nullvalue0/WiRSa/Pictures/2024-12-23T05_33_06.740Z-IMG_20241222_194014_2~2.jpg

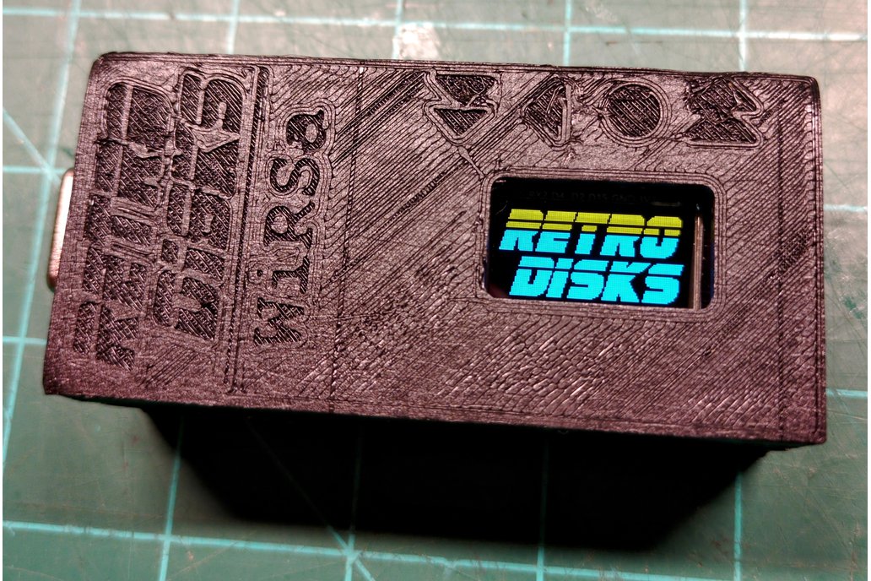
Pictures/2024-12-23T05_33_06.740Z-IMG_20241222_194014_2~2.jpg
