nullvalue0/WiRSa/Pictures/2024-12-23T05_37_01.366Z-IMG_20241222_223214_2~2.jpg

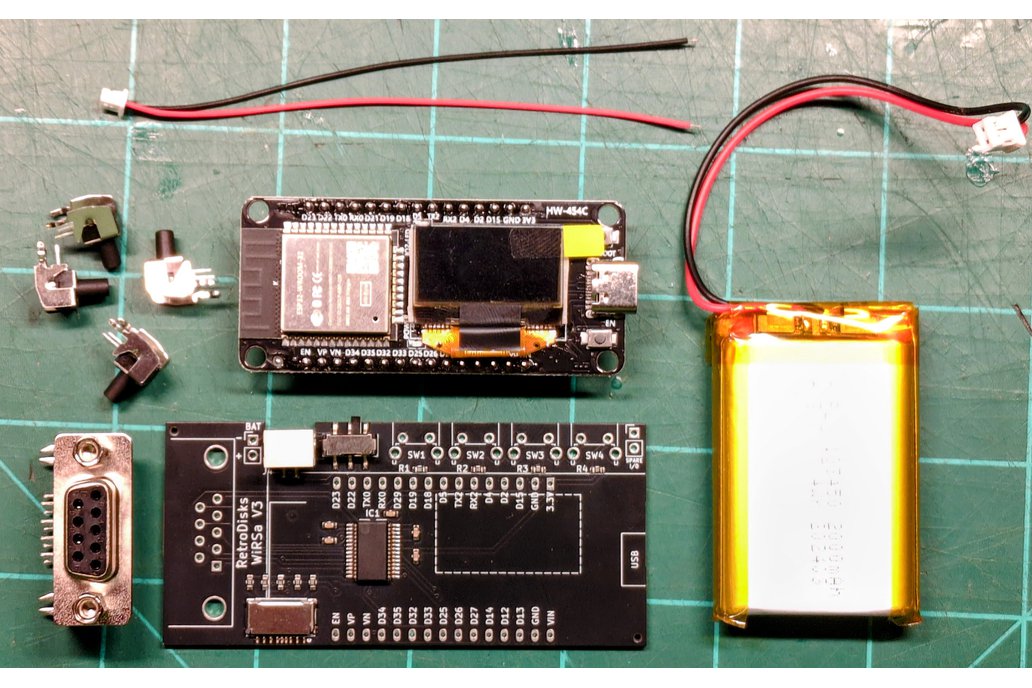
Pictures/2024-12-23T05_37_01.366Z-IMG_20241222_223214_2~2.jpg
