nullvalue0/WiRSa/Pictures/2024-12-24T02_32_21.541Z-IMG_20241223_105522_2~2(1).jpg

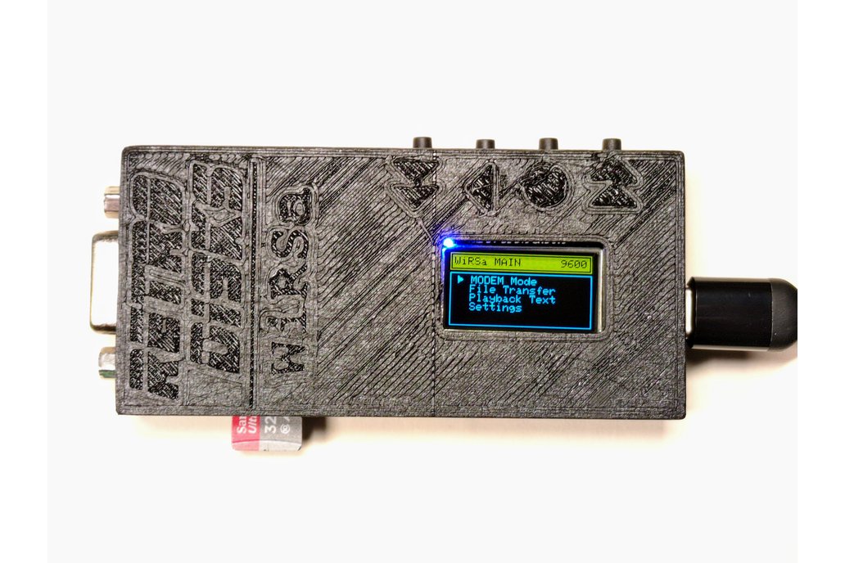
Pictures/2024-12-24T02_32_21.541Z-IMG_20241223_105522_2~2(1).jpg
