nullvalue0/WiRSa/Pictures/IMG_20241208_202616_2~2.jpg

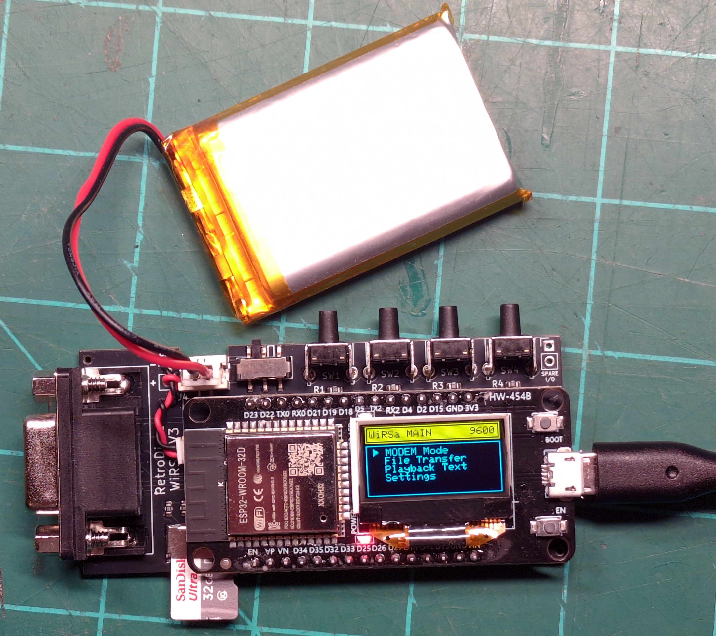
Pictures/IMG_20241208_202616_2~2.jpg
