nullvalue0/WiRSa/Pictures/PXL_20241209_022049034~2.jpg

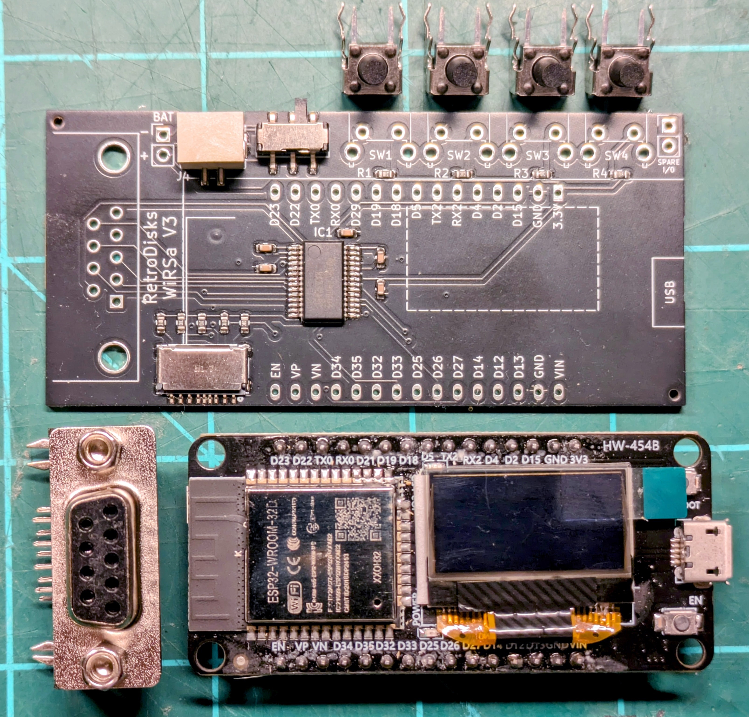
Pictures/PXL_20241209_022049034~2.jpg
