nullvalue0/WiRSa/Pictures/readme_image1.jpg

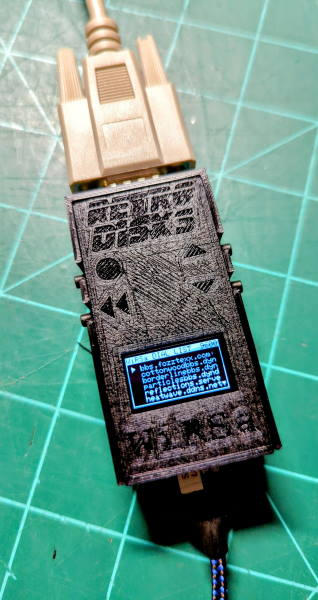
Pictures/readme_image1.jpg
