nullvalue0/WiRSa/Pictures/readme_image3.jpg

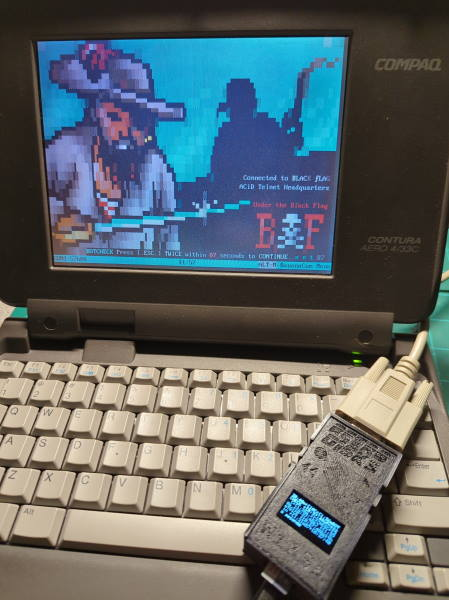
Pictures/readme_image3.jpg
