nullvalue0/WiRSa/Pictures/v2-IMG_20221031_160522~2 (8).jpg

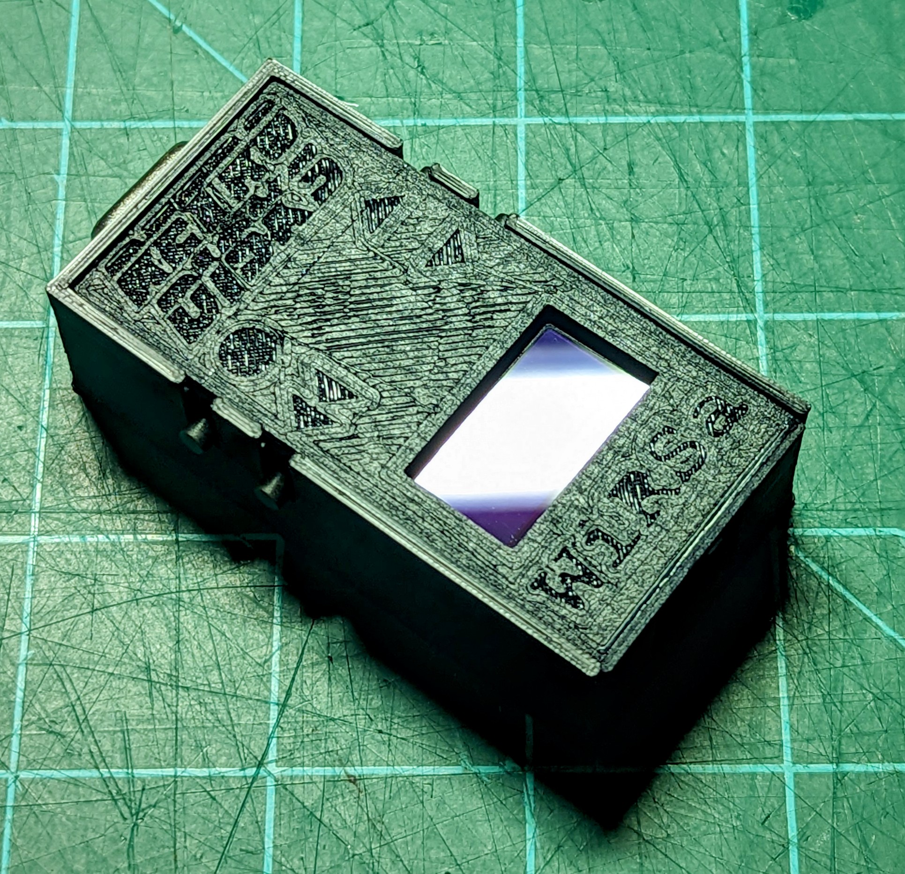
Pictures/v2-IMG_20221031_160522~2 (8).jpg
