nullvalue0/WiRSa/Pictures/v3render2.png

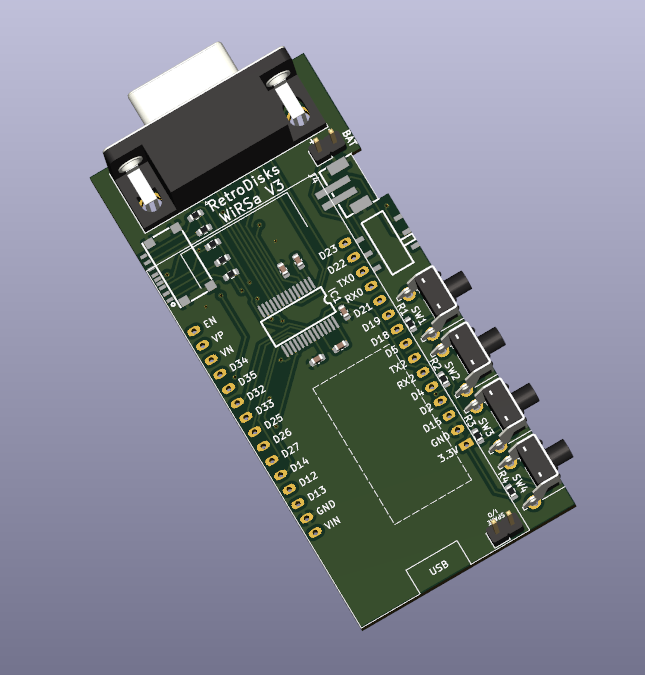
Pictures/v3render2.png
