nullvalue0/WiRSa/Firmware/include/ppp_lcp.h

// ============================================================================
// PPP Link Control Protocol (LCP) - RFC 1661
// ============================================================================
// Handles link establishment, configuration, and termination
// ============================================================================

#ifndef PPP_LCP_H
#define PPP_LCP_H

#include <Arduino.h>
#include "ppp.h"

// ============================================================================
// LCP Code Values (RFC 1661)
// ============================================================================

#define LCP_CONFIGURE_REQUEST   1
#define LCP_CONFIGURE_ACK       2
#define LCP_CONFIGURE_NAK       3
#define LCP_CONFIGURE_REJECT    4
#define LCP_TERMINATE_REQUEST   5
#define LCP_TERMINATE_ACK       6
#define LCP_CODE_REJECT         7
#define LCP_PROTOCOL_REJECT     8
#define LCP_ECHO_REQUEST        9
#define LCP_ECHO_REPLY          10
#define LCP_DISCARD_REQUEST     11

// ============================================================================
// LCP Option Types
// ============================================================================

#define LCP_OPT_MRU             1   // Maximum Receive Unit
#define LCP_OPT_ACCM            2   // Async Control Character Map
#define LCP_OPT_AUTH_PROTO      3   // Authentication Protocol
#define LCP_OPT_QUALITY         4   // Quality Protocol
#define LCP_OPT_MAGIC_NUMBER    5   // Magic Number (loop detection)
#define LCP_OPT_PFC             7   // Protocol Field Compression
#define LCP_OPT_ACFC            8   // Address/Control Field Compression

// ============================================================================
// LCP States (Simplified from RFC 1661)
// ============================================================================

enum LcpState {
    LCP_STATE_INITIAL,      // Link not started
    LCP_STATE_STARTING,     // Lower layer up, waiting to send config
    LCP_STATE_CLOSED,       // Link closed
    LCP_STATE_STOPPED,      // Link stopped (waiting for remote)
    LCP_STATE_CLOSING,      // Terminate-Request sent
    LCP_STATE_STOPPING,     // Terminate-Request sent, was open
    LCP_STATE_REQ_SENT,     // Configure-Request sent, waiting for response
    LCP_STATE_ACK_RCVD,     // Configure-Ack received (waiting for peer's request)
    LCP_STATE_ACK_SENT,     // Configure-Ack sent (waiting for our ACK)
    LCP_STATE_OPENED        // Link open and operational
};
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
